aclandmark/PCB111000_CP2102/AVR_freaks_first_posting/Firmware/cal_one_wire_comms/cal_one_wire_comms.ino

/*
The ATtiny1606 has a 1MHz peripheral clock.
It uses 2mS steps to drive the 8 digit display
 An extra 2mS is added for comms.
 A comms start pulse is sent to PB4 every 18mS.
 T1 clock of 1MHz counts to 18000 in this period
 Comms is allowed 10 times 0.2mS slots

Any inaccuracy in the ATtiny 1606 clock is compensated for by
a correction factor applied to the Atmega328 1-wire comms clock.
*/


#include "Project_header.h"                                 //Contains resources used by template and shared with programmer

int main (void) {

unsigned int PORT_1, PORT_2;

setup_328_HW;  
User_prompt;

if(User_response == 'R'){                                    //Drive display to check that calibration factor enables comms 
Serial.write("\r\nCalibration skipped: \
Press 'r' to calibrate\r\n" );
while(1){                                                    //Proj_1A
PORT_1 = 1;
PORT_2 = 0x8000;
for(int m = 0; m <=15; m++){
One_wire_Tx_2_integers(PORT_1, PORT_2);
_delay_ms(30);
PORT_1 = PORT_1 << 1;
PORT_2 = PORT_2 >> 1;}}}




/*******************************Calibration routine******************************************************************************/
/**************Measure time interval between successsive start pulses (generated by the 1606*************************************/
ATtiny1606_period = 0;                                      //Time between successive start pulses
for(int m = 0; m <= 99; m++){                               //Measure time 100 times 
if(!(m%10))Serial.write("  _");
measure_1606_mux_period;
ATtiny1606_period += TCNT1;}
ATtiny1606_period /= 100;                                    //Take average result

Serial.write("\r\n ATtiny1606 mux period \
in uS (should be 18000)\t");
Serial.print(ATtiny1606_period);
_delay_ms(5);


/**************Calculate correction factors to be applied to the Atmega display and comms locks*************************************/
Serial.write("\r\n\r\nCalculated comms correction \
factor\t");     
Comms_clock_correction = (ATtiny1606_period/9 - 2000)/10;
Serial.print (Comms_clock_correction);
_delay_ms(5);



/**************Generate table of correction factors and errors**************************/
Print_table_headings();

Comms_clock_correction -= 15;                                    //Print results for adjacent correction factors                                
for(int m = 0; m <= 20; m++){                                   //Confirms that the correction factor is not critical
Comms_clock = 200 + Comms_clock_correction;
Atmega_328_period =  Comms_clock * 90;

error = ATtiny1606_period - Atmega_328_period;
error_percent = 100 * error / ATtiny1606_period;

Print_results(Comms_clock_correction, Atmega_328_period, \
error, error_percent); 
Comms_clock_correction += 1;
_delay_ms(10);}
Serial.write("\r\n");


/**********************************Check for presence of a previous correction factor******************************************************/
if (((signed char)eeprom_read_byte((uint8_t*)0x3F7) > -50)
&&  ((signed char)eeprom_read_byte((uint8_t*)0x3F7) < 50) 
&& ((signed char)eeprom_read_byte((uint8_t*)0x3F7)
== (signed char)eeprom_read_byte((uint8_t*)0x3F6))) 
{User_correction_factor_previous = 
(signed char)eeprom_read_byte((uint8_t*)0x3F7);}
else User_correction_factor_previous = 0;


/********************************************User enters correction factor ****************************************************************/
User_correction_factor = 0;
Serial.write("\r\nUser correction? \r\nError of +4% recommended.  \
Terminate with -cr-.");
User_correction_factor = Int_from_KBD();



/******************************User correction factor saved to EEPROM and echoed to screen**************************************************/
eeprom_write_byte((uint8_t*)0x3F6, (User_correction_factor));                      //Save user cal in EEPROM 
eeprom_write_byte((uint8_t*)0x3F7, (User_correction_factor));

Serial.write("\r\nSaved to EEPROM");

comms_cal;
Atmega_328_period =  Comms_clock * 90;
error = signed (ATtiny1606_period - Atmega_328_period);
error_percent = 100 * error / ATtiny1606_period;

Print_results(User_correction_factor, Atmega_328_period, error, error_percent);


/************************************Print Previous User correction factor if avalibale*********************************************/
if(User_correction_factor_previous)
{
Serial.write("\r\nPrevious value of correction_factor was  ");
Serial.print(User_correction_factor_previous);
_delay_ms(5);}

Serial.write("\r\n\r\n");

SW_reset;
return 1;}


/**********************************************************************************************/
void Print_results(int Comms_clock_correction,  int Atmega_328_period, long error, long error_percent)
{Serial.write("\r\n    ");
Serial.print (Comms_clock_correction);
_delay_ms(5);
Serial.write("\t     ");
Serial.print (Atmega_328_period);
_delay_ms(5);
Serial.write("\t     ");
Serial.print (error);
_delay_ms(5);
Serial.write("\t  ");
Serial.print (error_percent);
_delay_ms(25);}



/**********************************************************************************************/
void Print_table_headings(void)
{Serial.write("\r\n\r\nCorrection    TCNT1\t    Error\terror%");}
