aclandmark/PCB111000_CP2102/AVR_freaks_first_posting/Firmware/CP2102_UPDI_Programmer/Resources_User_app/Project_subroutines.c

/*************************************************************************************************************/
void backup_the_display(char segment, char digit_num){
display_bkp[segment - 'a'] = display_bkp[segment - 'a'] ^ (1 << digit_num);}




/*************************************************************************************************************/
unsigned int PRN_16bit_GEN(unsigned int start){																//Google LFSR
unsigned int bit, lfsr;

if(!(start)) lfsr = (eeprom_read_byte((uint8_t*)(0x3F2)) << 8) + eeprom_read_byte((uint8_t*)(0x3F3));
else lfsr = start;
bit = (( lfsr >> 0) ^ (lfsr >> 2) ^ (lfsr >> 3) ^ (lfsr >> 5)) & 1;
lfsr = (lfsr >> 1) | (bit << 15);
if(!(start)){
eeprom_write_byte((uint8_t*)(0x3F2),(lfsr>>8));
eeprom_write_byte((uint8_t*)(0x3F3),lfsr);}

return lfsr;}
