aclandmark/PCB111000_CP2102/AVR_freaks_first_posting/Firmware/CP2102_UPDI_Programmer/Resources_User_app.h

#include <avr/io.h>
#include <stdlib.h>
#include <avr/interrupt.h>
#include <avr/wdt.h>
#include <avr/eeprom.h>


#include "Resources_User_app\Resources_user_app.h"
#include "Resources_User_app\One_wire_transactions.c"
#include "Resources_User_app\Resources_shared.h"
#include "Resources_User_app\Resources_shared.c"

#include "Resources_User_app\Project_subroutines.c"
